promesoft/KicadJE_LFO_1/Kicad_LFO_1/DSC_2449.JPG

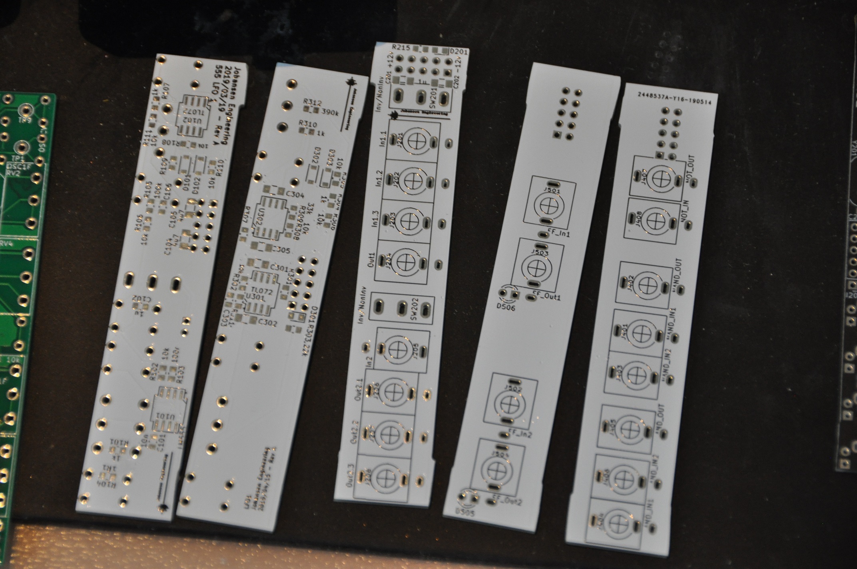
Kicad_LFO_1/DSC_2449.JPG
